bountylabs/blocks-with-screens/pcb/blocks-with-screens.sch

## EAGLE design pcb/blocks-with-screens.sch (2019-09-18)

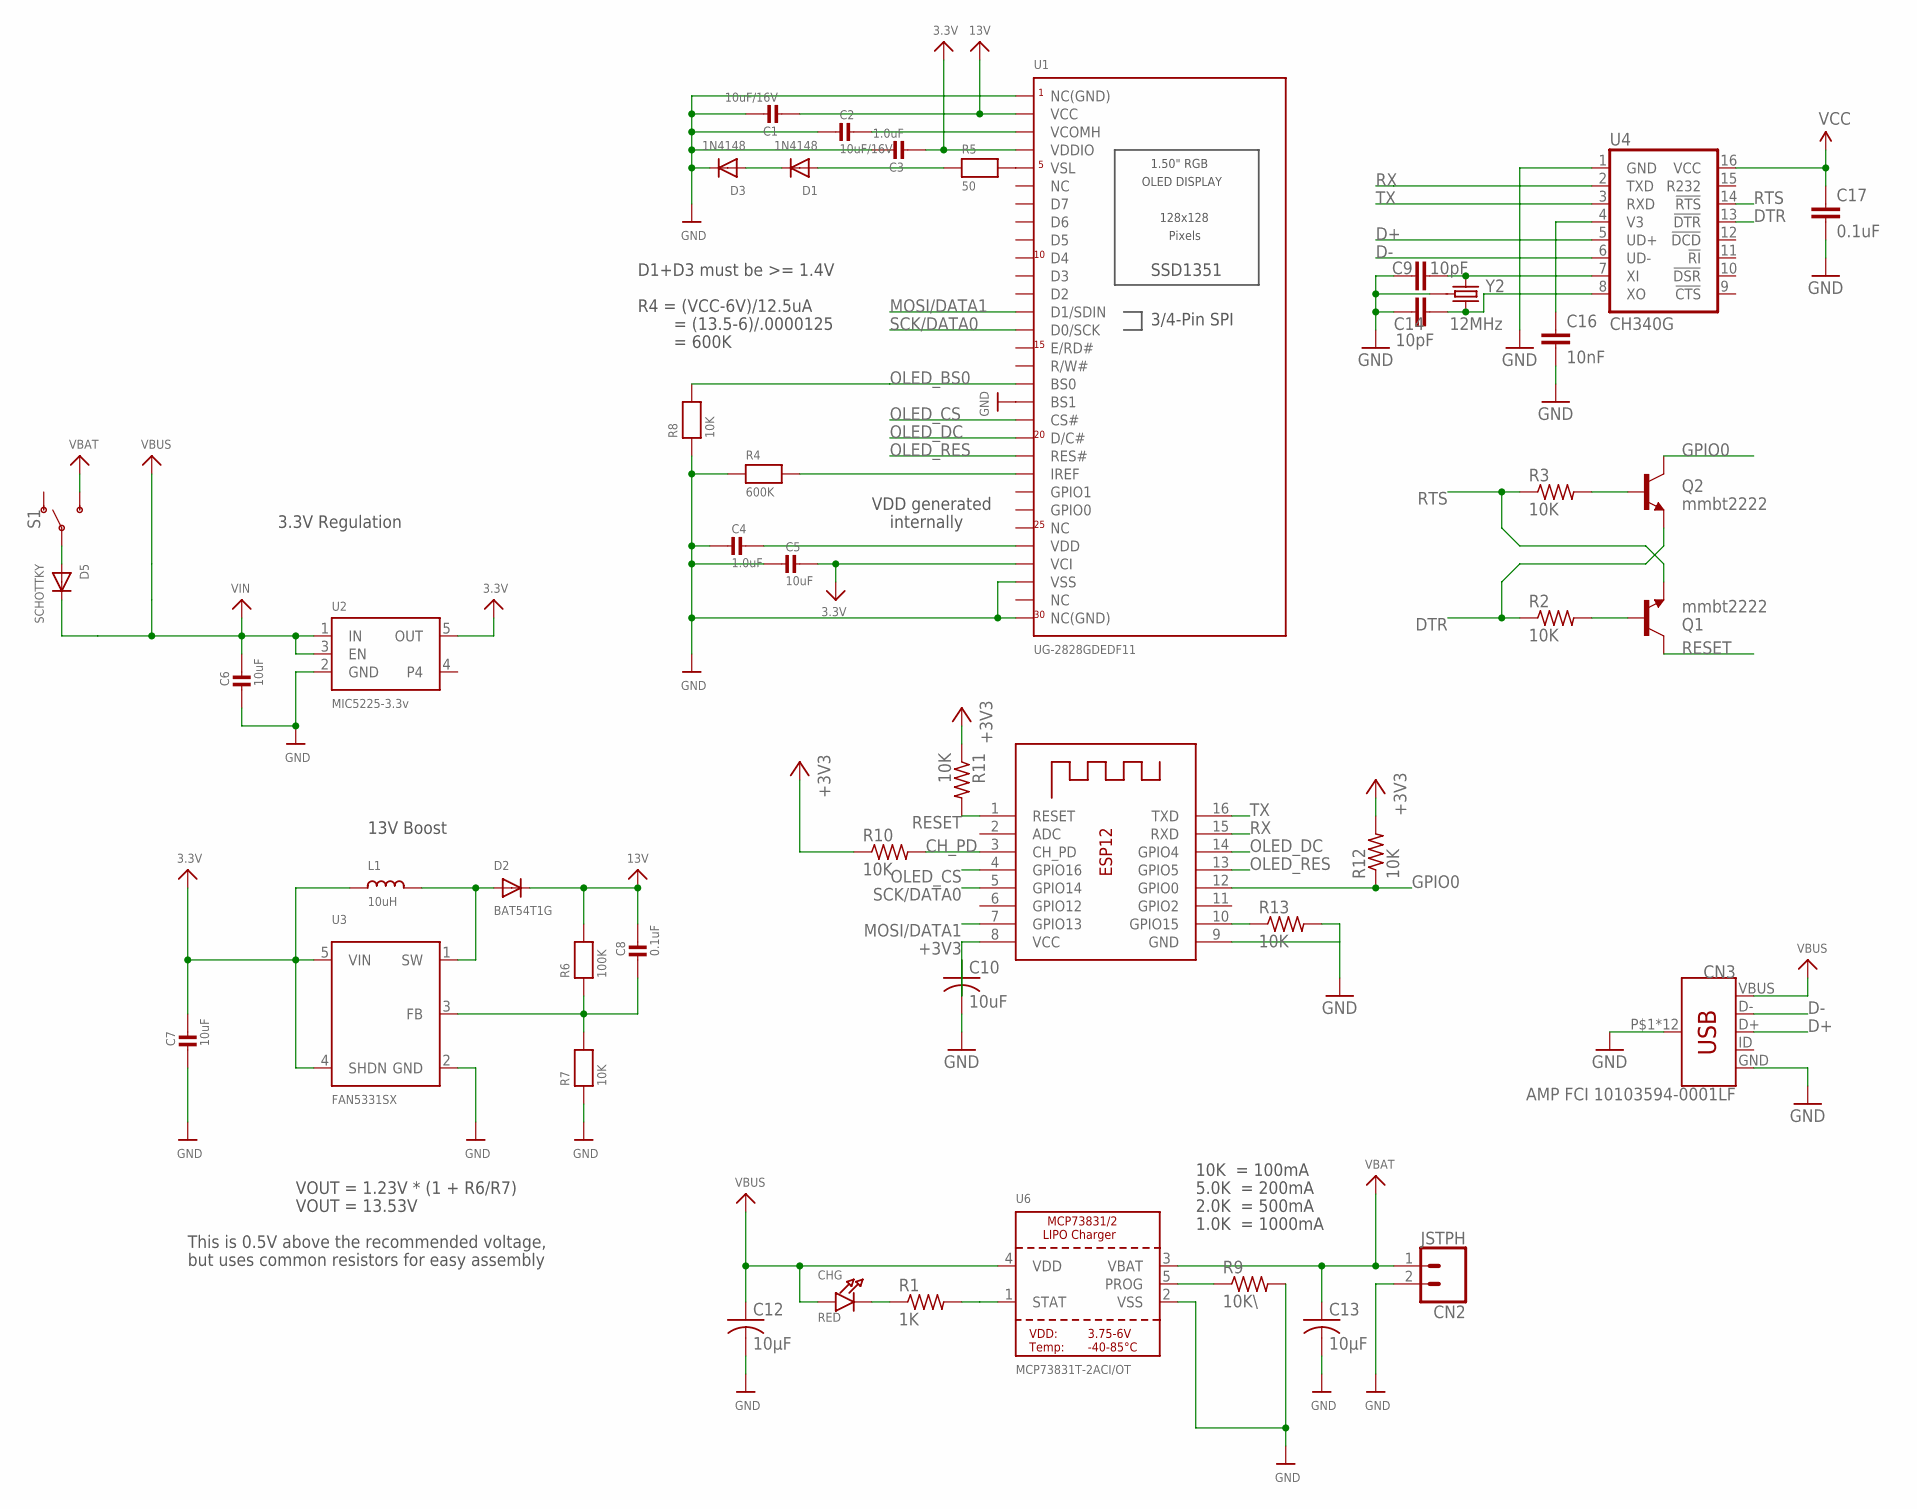
[picture p15: schematic blocks-with-screens.sch]

Parts:
C1, C2: 10uF/16V; 0805
C3, C4: 1.0uF; 0805
C5, C6, C7: 10uF; 0805
C8: 0.1uF; 0805
C9, C14: 10pF; 0603-CAP
C10: 10uF; C0805
C12, C13: 10µF; C0805
C16: 10nF; 0603-CAP
C17: 0.1uF; 0603-CAP
CHG: RED; CHIPLED_0805_NOOUTLINE
CN2: JSTPH; 1X02
CN3: AMP FCI 10103594-0001LF; USB-MICROB-PTH
D1, D3: 1N4148; SOD-323
D2: BAT54T1G; SOD-123
D5: SCHOTTKY; SOD-123FL
L1: 10uH; INDUCTOR_1007
Q1, Q2: mmbt2222; SOT23-3
R1: 1K; R0805
R2, R3: 10K; R0603
R4: 600K; 0805
R5: 50; 0805
R6: 100K; 0805
R7, R8: 10K; 0805
R9: 10K\; R0805
R10, R11, R12, R13: 10K; R0805
S1: SWITCH-SPDT-SMD-RIGHT-ANGLE; SWITCH_SPST_SMD_A
U1: UG-2828GDEDF11; FPC_XF2M-3015-1A
U2: MIC5225-3.3v; SOT23-5
U3: FAN5331SX; SOT23-5@1
U4: CH340G; SO016
U6: MCP73831T-2ACI/OT; SOT23-5
X1: ESP-12
Y2: 12MHz; CRYSTAL-SMD-3.2X2.5

Connections:
3.3V: C3.2, C5.1, C7.1, L1.P$1 (1), U1.P$4 (VCI), U1.P$27 (VDDIO), U2.5 (OUT), U3.4 (SHDN), U3.5 (VIN)
13V: C1.2, C8.1, D2.C, R6.2, U1.P$29 (VCC)
+3V3: C10.1, R10.1, R11.1, R12.2, X1.8 (VCC)
CH_PD: R10.2, X1.3 (CH_PD)
D+: CN3.D+, U4.5 (UD+)
D-: CN3.D-, U4.6 (UD-)
DTR: Q2.2 (E), R2.1, U4.13 (!DTR)
GND: C1.1, C2.2, C3.1, C4.2, C5.2, C6.2, C7.2, C9.1, C10.2, C12.2, C13.2, C14.1, C16.2, C17.2, CN2.2, CN3.GND, CN3.P$1 (SHIELD), D3.C, R4.1, R7.1, R8.1, R9.2, R13.2, U1.P$1 (NC(GND)), U1.P$3 (VSS), U1.P$13 (BS1), U1.P$30 (NC(GND)), U2.2 (GND), U3.2 (GND), U4.1 (GND), U6.2 (VSS), X1.9 (GND), Y2.2 (GND)
GPIO0: Q2.3 (C), R12.1, X1.12 (GPIO0)
IREF: R4.2, U1.P$9 (IREF)
MOSI/DATA1: U1.P$18 (D1/SDIN), X1.7 (GPIO13)
unnamed: CHG.C, R1.1
unnamed: C4.1, U1.P$5 (VDD)
unnamed: R1.2, U6.1 (STAT)
unnamed: D2.A, L1.P$2 (2), U3.1 (SW)
unnamed: R5.2, U1.P$26 (VSL)
unnamed: D1.A, R5.1
unnamed: C8.2, R6.1, R7.2, U3.3 (FB)
unnamed: R9.1, U6.5 (PROG)
unnamed: C14.2, U4.8 (XO), Y2.3 (2)
unnamed: D1.C, D3.A
unnamed: C9.2, U4.7 (XI), Y2.1
unnamed: Q1.1 (B), R2.2
unnamed: Q2.1 (B), R3.2
unnamed: R13.1, X1.10 (GPIO15)
unnamed: D5.A, S1.2
OLED_BS0: R8.2, U1.P$14 (BS0)
OLED_CS: U1.P$12 (CS#), X1.4 (GPIO16)
OLED_DC: U1.P$11 (D/C#), X1.14 (GPIO4)
OLED_RES: U1.P$10 (RES#), X1.13 (GPIO5)
RESET: Q1.3 (C), R11.2, X1.1 (RESET)
RTS: Q1.2 (E), R3.1, U4.14 (!RTS)
RX: U4.2 (TXD), X1.15 (RXD)
SCK/DATA0: U1.P$17 (D0/SCK), X1.5 (GPIO14)
TX: U4.3 (RXD), X1.16 (TXD)
V3: C16.1, U4.4 (V3)
VBAT: C13.1, CN2.1, S1.3 (S), U6.3 (VBAT)
VBUS: C6.1, C12.1, CHG.A, CN3.VBUS, D5.C, U2.1 (IN), U2.3 (EN), U6.4 (VDD)
VCC: C17.1, U4.16 (VCC)
VCOMH: C2.1, U1.P$28 (VCOMH)

Notes on the sheet:
3.3V Regulation
VOUT = 1.23V * (1 + R6/R7)
VOUT = 13.53V
This is 0.5V above the recommended voltage,
but uses common resistors for easy assembly
13V Boost
R4 = (VCC-6V)/12.5uA
= (13.5-6)/.0000125
= 600K
D1+D3 must be >= 1.4V
VDD generated
internally
10K = 100mA
5.0K = 200mA
2.0K = 500mA
1.0K = 1000mA
