bountylabs/blocks-with-screens/blockware/snake/src/main.cpp

#include <Adafruit_GFX.h>
#include <Adafruit_SSD1351.h>
#include <ESP8266WebServer.h>
#include <ESP8266WiFi.h>
#include <DefaultConfig.h>

#define BLUE 0xFF
#define RED 0xF800
#define MESSAGE_SPEED 2
#define INITIAL_SNAKE_LENGTH 1
#define SCALE_FACTOR 8
#define BOARD_SIZE 8
#define UP 1
#define RIGHT 2
#define DOWN 3
#define LEFT 4
#define HTML "<title>Snake</title><meta content=\"width=device-width,initial-scale=1\"name=viewport><script>function makeRequest(e){request=new XMLHttpRequest,request.open(\"GET\",e),request.send()}document.onkeydown=function(e){\"38\"==(e=e||window.event).keyCode?makeRequest(\"/up.html\"):\"40\"==e.keyCode?makeRequest(\"/down.html\"):\"37\"==e.keyCode?makeRequest(\"/left.html\"):\"39\"==e.keyCode&&makeRequest(\"/right.html\")}</script><style>body{position:relative;width:100%;min-height:100vh;min-height:-webkit-fill-available;font-size:32px;font-family:Futura;padding:0;margin:0}.container{position:relative;text-align:center;margin:auto;top:50%;transform:translateY(-50%)}button{display:inline-block;width:50px;height:50px;border-radius:25px;color:#fff;outline:0;border:none;margin-bottom:20px;font-family:Futura}button:active{opacity:.5}.up{background:#466cb2}.down{background:#e1b551;margin-left:20px;margin-right:20px}.left{background:#16a674}.right{background:#ee565d}</style><div class=container>Snake<br><br><button class=up onclick='makeRequest(\"/up.html\")'>Up</button><br><button class=left onclick='makeRequest(\"/left.html\")'>Left</button> <button class=down onclick='makeRequest(\"/down.html\")'>Down</button> <button class=right onclick='makeRequest(\"/right.html\")'>Right</button></div>"

/**
 * Forward defines because C++
 */
void drawGameBoardCell(int oldX, int oldY, byte on);
void unrollSnake();
void showScoreMessage(int score);
void fixEdge();
void handleRight();
void handleLeft();
void handleUp();
void handleDown();
void handleRoot();

/**
 * Bitmaps
 */
const PROGMEM bool snakeMessage[8][56] = {
  {0, 0, 0, 0, 0, 0, 0, 0, 0, 0, 0, 0, 0, 0, 0, 0, 0, 0, 0, 0, 0, 0, 0, 0, 0, 0, 0, 0, 0, 0, 0, 0, 0, 0, 0, 0, 0, 0, 0, 0, 0, 0, 0, 0, 0, 0, 0, 0, 0, 0, 0, 0, 0, 0, 0, 0},
  {0, 0, 0, 0, 0, 0, 0, 0, 0, 1, 1, 1, 1, 0, 0, 0, 1, 1, 0, 0, 0, 1, 1, 0, 0, 0, 1, 1, 1, 1, 0, 0, 0, 1, 1, 0, 0, 1, 1, 0, 0, 1, 1, 1, 1, 1, 1, 0, 0, 0, 0, 0, 0, 0, 0, 0},
  {0, 0, 0, 0, 0, 0, 0, 0, 1, 1, 0, 0, 1, 1, 0, 0, 1, 1, 1, 0, 0, 1, 1, 0, 0, 1, 1, 0, 0, 1, 1, 0, 0, 1, 1, 0, 1, 1, 0, 0, 0, 1, 1, 0, 0, 0, 0, 0, 0, 0, 0, 0, 0, 0, 0, 0},
  {0, 0, 0, 0, 0, 0, 0, 0, 1, 1, 0, 0, 0, 0, 0, 0, 1, 1, 1, 1, 0, 1, 1, 0, 0, 1, 1, 0, 0, 1, 1, 0, 0, 1, 1, 1, 1, 0, 0, 0, 0, 1, 1, 0, 0, 0, 0, 0, 0, 0, 0, 0, 0, 0, 0, 0},
  {0, 0, 0, 0, 0, 0, 0, 0, 0, 1, 1, 1, 1, 0, 0, 0, 1, 1, 0, 1, 1, 1, 1, 0, 0, 1, 1, 1, 1, 1, 1, 0, 0, 1, 1, 1, 0, 0, 0, 0, 0, 1, 1, 1, 1, 1, 0, 0, 0, 0, 0, 0, 0, 0, 0, 0},
  {0, 0, 0, 0, 0, 0, 0, 0, 0, 0, 0, 0, 1, 1, 0, 0, 1, 1, 0, 0, 1, 1, 1, 0, 0, 1, 1, 0, 0, 1, 1, 0, 0, 1, 1, 1, 1, 0, 0, 0, 0, 1, 1, 0, 0, 0, 0, 0, 0, 0, 0, 0, 0, 0, 0, 0},
  {0, 0, 0, 0, 0, 0, 0, 0, 1, 1, 0, 0, 1, 1, 0, 0, 1, 1, 0, 0, 0, 1, 1, 0, 0, 1, 1, 0, 0, 1, 1, 0, 0, 1, 1, 0, 1, 1, 0, 0, 0, 1, 1, 0, 0, 0, 0, 0, 0, 0, 0, 0, 0, 0, 0, 0},
  {0, 0, 0, 0, 0, 0, 0, 0, 0, 1, 1, 1, 1, 0, 0, 0, 1, 1, 0, 0, 0, 1, 1, 0, 0, 1, 1, 0, 0, 1, 1, 0, 0, 1, 1, 0, 0, 1, 1, 0, 0, 1, 1, 1, 1, 1, 1, 0, 0, 0, 0, 0, 0, 0, 0, 0}
};

const PROGMEM bool gameOverMessage[8][90] = {
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
  {0, 0, 0, 0, 0, 0, 0, 0, 0, 1, 1, 1, 1, 0, 0, 0, 0, 1, 1, 1, 1, 0, 0, 0, 0, 1, 1, 1, 1, 0, 0, 0, 1, 1, 0, 0, 1, 1, 0, 0, 1, 1, 1, 1, 1, 1, 0, 0, 0, 0, 0, 0, 0, 0, 0, 0, 0, 0}
};

const PROGMEM bool digits[][8][8] = {
  {
    {0, 0, 0, 0, 0, 0, 0, 0},
    {0, 0, 1, 1, 1, 1, 0, 0},
    {0, 1, 1, 0, 0, 1, 1, 0},
    {0, 1, 1, 0, 1, 1, 1, 0},
    {0, 1, 1, 1, 0, 1, 1, 0},
    {0, 1, 1, 0, 0, 1, 1, 0},
    {0, 1, 1, 0, 0, 1, 1, 0},
    {0, 0, 1, 1, 1, 1, 0, 0}
  },
  {
    {0, 0, 0, 0, 0, 0, 0, 0},
    {0, 0, 0, 1, 1, 0, 0, 0},
    {0, 0, 0, 1, 1, 0, 0, 0},
    {0, 0, 1, 1, 1, 0, 0, 0},
    {0, 0, 0, 1, 1, 0, 0, 0},
    {0, 0, 0, 1, 1, 0, 0, 0},
    {0, 0, 0, 1, 1, 0, 0, 0},
    {0, 1, 1, 1, 1, 1, 1, 0}
  },
  {
    {0, 0, 0, 0, 0, 0, 0, 0},
    {0, 0, 1, 1, 1, 1, 0, 0},
    {0, 1, 1, 0, 0, 1, 1, 0},
    {0, 0, 0, 0, 0, 1, 1, 0},
    {0, 0, 0, 0, 1, 1, 0, 0},
    {0, 0, 1, 1, 0, 0, 0, 0},
    {0, 1, 1, 0, 0, 0, 0, 0},
    {0, 1, 1, 1, 1, 1, 1, 0}
  },
  {
    {0, 0, 0, 0, 0, 0, 0, 0},
    {0, 0, 1, 1, 1, 1, 0, 0},
    {0, 1, 1, 0, 0, 1, 1, 0},
    {0, 0, 0, 0, 0, 1, 1, 0},
    {0, 0, 0, 1, 1, 1, 0, 0},
    {0, 0, 0, 0, 0, 1, 1, 0},
    {0, 1, 1, 0, 0, 1, 1, 0},
    {0, 0, 1, 1, 1, 1, 0, 0}
  },
  {
    {0, 0, 0, 0, 0, 0, 0, 0},
    {0, 0, 0, 0, 1, 1, 0, 0},
    {0, 0, 0, 1, 1, 1, 0, 0},
    {0, 0, 1, 0, 1, 1, 0, 0},
    {0, 1, 0, 0, 1, 1, 0, 0},
    {0, 1, 1, 1, 1, 1, 1, 0},
    {0, 0, 0, 0, 1, 1, 0, 0},
    {0, 0, 0, 0, 1, 1, 0, 0}
  },
  {
    {0, 0, 0, 0, 0, 0, 0, 0},
    {0, 1, 1, 1, 1, 1, 1, 0},
    {0, 1, 1, 0, 0, 0, 0, 0},
    {0, 1, 1, 1, 1, 1, 0, 0},
    {0, 0, 0, 0, 0, 1, 1, 0},
    {0, 0, 0, 0, 0, 1, 1, 0},
    {0, 1, 1, 0, 0, 1, 1, 0},
    {0, 0, 1, 1, 1, 1, 0, 0}
  },
  {
    {0, 0, 0, 0, 0, 0, 0, 0},
    {0, 0, 1, 1, 1, 1, 0, 0},
    {0, 1, 1, 0, 0, 1, 1, 0},
    {0, 1, 1, 0, 0, 0, 0, 0},
    {0, 1, 1, 1, 1, 1, 0, 0},
    {0, 1, 1, 0, 0, 1, 1, 0},
    {0, 1, 1, 0, 0, 1, 1, 0},
    {0, 0, 1, 1, 1, 1, 0, 0}
  },
  {
    {0, 0, 0, 0, 0, 0, 0, 0},
    {0, 1, 1, 1, 1, 1, 1, 0},
    {0, 1, 1, 0, 0, 1, 1, 0},
    {0, 0, 0, 0, 1, 1, 0, 0},
    {0, 0, 0, 0, 1, 1, 0, 0},
    {0, 0, 0, 1, 1, 0, 0, 0},
    {0, 0, 0, 1, 1, 0, 0, 0},
    {0, 0, 0, 1, 1, 0, 0, 0}
  },
  {
    {0, 0, 0, 0, 0, 0, 0, 0},
    {0, 0, 1, 1, 1, 1, 0, 0},
    {0, 1, 1, 0, 0, 1, 1, 0},
    {0, 1, 1, 0, 0, 1, 1, 0},
    {0, 0, 1, 1, 1, 1, 0, 0},
    {0, 1, 1, 0, 0, 1, 1, 0},
    {0, 1, 1, 0, 0, 1, 1, 0},
    {0, 0, 1, 1, 1, 1, 0, 0}
  },
  {
    {0, 0, 0, 0, 0, 0, 0, 0},
    {0, 0, 1, 1, 1, 1, 0, 0},
    {0, 1, 1, 0, 0, 1, 1, 0},
    {0, 1, 1, 0, 0, 1, 1, 0},
    {0, 0, 1, 1, 1, 1, 1, 0},
    {0, 0, 0, 0, 0, 1, 1, 0},
    {0, 1, 1, 0, 0, 1, 1, 0},
    {0, 0, 1, 1, 1, 1, 0, 0}
  }
};

/**
 * Global variables.
 */
ESP8266WebServer server(80);
IPAddress IP(192,168,4,15);
IPAddress mask = (255, 255, 255, 0);
int connected = 0;
Adafruit_SSD1351 display = Adafruit_SSD1351(SCREEN_WIDTH, SCREEN_HEIGHT, &SPI, CS_PIN, DC_PIN, RST_PIN);

struct Point {
  int row = 0, col = 0;
  Point(int row = 0, int col = 0): row(row), col(col) {}
};

/**
 * Game state
 */
int gameboard[BOARD_SIZE][BOARD_SIZE] = {};
bool win = false;
bool gameOver = false;
Point snake;  // primary snake head coordinates (snake head), it will be randomly generated
Point food(-1, -1); // food is not anywhere yet

/**
 * Snake parameters
 */
int snakeLength = INITIAL_SNAKE_LENGTH; // choosed by the user in the config section
int snakeSpeed = 1; // will be set according to potentiometer value, cannot be 0
int snakeDirection = 0; // if it is 0, the snake does not move

/**
 * Sets up WiFi for the block. This enables the block to serve as the access point.
 */
void setUpWifi() {
  WiFi.mode(WIFI_AP);
  WiFi.softAP("Snake", "");
  WiFi.softAPConfig(IP, IP, mask);
}

/**
 * Sets up Web server routing. The web pages listed will be used to serve pages that
 * clients can visit to control the snake.
 */
void setUpRouting() {
  server.on("/", handleRoot);
  server.on("/up.html", handleUp);
  server.on("/down.html", handleDown);
  server.on("/left.html", handleLeft);
  server.on("/right.html", handleRight);
  server.begin();
}

/**
 * Handles when the client visits "/"
 */
void handleRoot() {
  connected = 1;
  server.send(200, "text/html", HTML);
}


/**
 * Handles when the client visits "/up"
 */
void handleUp() {
  snakeDirection = UP;
  server.send(200, "text/html", HTML);
}

/**
 * Handles when the client visits "/down"
 */
void handleDown() {
  snakeDirection = DOWN;
  server.send(200, "text/html", HTML);
}

/**
 * Handles when the client visits "/left"
 */
void handleLeft() {
  snakeDirection = LEFT;
  server.send(200, "text/html", HTML);
}

/**
 * Handles when the client visits "/right"
 */
void handleRight() {
  snakeDirection = RIGHT;
  server.send(200, "text/html", HTML);
}

/**
 * Initializes the game
 */
void initializeGame() {
  randomSeed(analogRead(A0));
  snake.row = random(8);
  snake.col = random(8);
}

/**
 * Shows the bootscreen.
 */
void showSnakeMessage() {
  [&] {
    for (int d = 0; d < sizeof(snakeMessage[0]) - 7; d++) {
      for (int col = 0; col < 8; col++) {
        delay(MESSAGE_SPEED);
        for (int row = 0; row < 8; row++) {
          // this reads the byte from the PROGMEM and displays it on the screen
          drawGameBoardCell(row, col, pgm_read_byte(&(snakeMessage[row][col + d])));
        }
        if (connected) {
          return;
        }
      }
    }
  }();
}

/**
 * Generates a food cell if one does not already exist.
 */
void generateFood() {
  if (food.row == -1 || food.col == -1) {
    // self-explanatory
    if (snakeLength >= 64) {
      win = true;
      return; // prevent the food generator from running, in this case it would run forever, because it will not be able to find a pixel without a snake
    }

    // generate food until it is in the right position
    do {
      food.col = random(8);
      food.row = random(8);
    } while (gameboard[food.row][food.col] > 0);
  }
}


/**
 * Changes movement of the snake to react to user input.
 */
void reactToInput() {
  int previousDirection = snakeDirection; // save the last direction

  delay(snakeSpeed);
  
  // ignore directional change by 180 degrees (no effect for non-moving snake)
  snakeDirection + 2 == previousDirection && previousDirection != 0 ? snakeDirection = previousDirection : 0;
  snakeDirection - 2 == previousDirection && previousDirection != 0 ? snakeDirection = previousDirection : 0;
  
  // intelligently blink with the food
  drawGameBoardCell(food.row, food.col, millis() % 100 < 50 ? 1 : 0);
}

/**
 * Calculates location of snake.
 */
void calculateSnake() {
   // decrement all the snake body segments, if segment is 0, turn the corresponding led off
  for (int row = 0; row < 8; row++) {
    for (int col = 0; col < 8; col++) {
      // if there is a body segment, decrement it's value
      if (gameboard[row][col] > 0 ) {
        gameboard[row][col]--;
      }

      // display the current pixel
      drawGameBoardCell(row, col, gameboard[row][col] == 0 ? 0 : 1);
    }
  }
  
  switch (snakeDirection) {
    case UP: {
      snake.row--;
      fixEdge();
      drawGameBoardCell(snake.row, snake.col, 1);
      break;
    }
    case RIGHT: {
      snake.col++;
      fixEdge();
      drawGameBoardCell(snake.row, snake.col, 1);
      break;
    }
    case DOWN: {
      snake.row++;
      fixEdge();
      drawGameBoardCell(snake.row, snake.col, 1);
      break;
    }
    case LEFT: {
      snake.col--;
      fixEdge();
      drawGameBoardCell(snake.row, snake.col, 1);
      break;
    }
    default: {
      return;
    }
  }

  // if there is a snake body segment, this will cause the end of the game (snake must be moving)
  if (gameboard[snake.row][snake.col] > 1 && snakeDirection != 0) {
    gameOver = true;
    return;
  }

  // check if the food was eaten
  if (snake.row == food.row && snake.col == food.col) {
    food.row = -1; // reset food
    food.col = -1;

    // increment snake length
    snakeLength++;

    // increment all the snake body segments
    for (int row = 0; row < 8; row++) {
      for (int col = 0; col < 8; col++) {
        if (gameboard[row][col] > 0 ) {
          gameboard[row][col]++;
        }
      }
    }
  }

  // add new segment at the snake head location
  gameboard[snake.row][snake.col] = snakeLength + 1; // will be decremented in a moment
}

/**
 * Handles a change in the game's state and displays appropriate messages if necessary.
 */
void handleGameStates() {
  if (gameOver || win) {
    unrollSnake();

    showScoreMessage(snakeLength - INITIAL_SNAKE_LENGTH);
    
    // re-init the game
    win = false;
    gameOver = false;
    snake.row = random(8);
    snake.col = random(8);
    food.row = -1;
    food.col = -1;
    snakeLength = INITIAL_SNAKE_LENGTH;
    snakeDirection = 0;
    memset(gameboard, 0, sizeof(gameboard[0][0]) * 8 * 8);
  }
}

/**
 * Runs the game loop. Call this on every loop() iteration once the client has
 * connected.
 */
void runGameLoop() {
  generateFood();     // if there is no food, generate one
  reactToInput();     // watches joystick movements & blinks with food
  calculateSnake();   // calculates snake parameters
  handleGameStates();
}

/**
 * Draws the specified cell in the game board along with whether it is on or
 * off to the screen. 
 */
void drawGameBoardCell(int oldX, int oldY, byte on) {
  int x = oldY;
  int y = oldX;

  int xOffset = (display.width() - (SCALE_FACTOR * BOARD_SIZE)) / 2;
  int yOffset = (display.height() - (SCALE_FACTOR * BOARD_SIZE)) / 2;

  for (int pixelX = 0; pixelX < SCALE_FACTOR / 2; pixelX++) {
    for (int pixelY = 0; pixelY < SCALE_FACTOR / 2; pixelY++) {
      display.drawPixel(SCALE_FACTOR * x + pixelX + xOffset, SCALE_FACTOR * y + pixelY + yOffset, on == 0 ? 0x00 :0xFF);
    }
  }
}

/**
 * Draws the bounds of the game board.
 */
void drawBounds() {
  int xOffset = (display.width() - (SCALE_FACTOR * BOARD_SIZE)) / 2;
  int yOffset = (display.height() - (SCALE_FACTOR * BOARD_SIZE)) / 2;
  
  for (int pixelY = 0; pixelY < display.height(); pixelY++) {
    display.drawPixel(xOffset - 1, pixelY, RED);
  }

  for (int pixelY = 0; pixelY < display.height(); pixelY++) {
    display.drawPixel(display.width() - xOffset, pixelY, RED);
  }

  for (int pixelX = 0; pixelX < display.width(); pixelX++) {
    display.drawPixel(pixelX, yOffset - 1, RED);
  }

  for (int pixelX = 0; pixelX < display.width(); pixelX++) {
    display.drawPixel(pixelX, display.height() - yOffset, RED);
  }
}

/**
 * Wraps the snake to the other side of the screen if needed.
 */
void fixEdge() {
  snake.col < 0 ? snake.col += 8 : 0;
  snake.col > 7 ? snake.col -= 8 : 0;
  snake.row < 0 ? snake.row += 8 : 0;
  snake.row > 7 ? snake.row -= 8 : 0;
}

/**
 * Unrolls the snake.
 */
void unrollSnake() {
  // switch off the food LED
  drawGameBoardCell(food.row, food.col, 0);
  delay(800);
  // flash the screen 5 times
  for (int i = 0; i < 5; i++) {
    // invert the screen
    for (int row = 0; row < 8; row++) {
      for (int col = 0; col < 8; col++) {
        drawGameBoardCell(row, col, gameboard[row][col] == 0 ? 1 : 0);
      }
    }
    delay(20);
    // invert it back
    for (int row = 0; row < 8; row++) {
      for (int col = 0; col < 8; col++) {
        drawGameBoardCell(row, col, gameboard[row][col] == 0 ? 0 : 1);
      }
    }
    delay(50);
  }
  delay(600);
  for (int i = 1; i <= snakeLength; i++) {
    for (int row = 0; row < 8; row++) {
      for (int col = 0; col < 8; col++) {
        if (gameboard[row][col] == i) {
          drawGameBoardCell(row, col, 0);
          delay(100);
        }
      }
    }
  }
}

/**
 * Shows the score message along with the score once the game is over.
 */
void showScoreMessage(int score) {
  if (score < 0 || score > 99) return;

  // specify score digits
  int second = score % 10;
  int first = (score / 10) % 10;

  [&] {
    for (int d = 0; d < sizeof(scoreMessage[0]) + 2 * sizeof(digits[0][0]); d++) {
      for (int col = 0; col < 8; col++) {
        delay(MESSAGE_SPEED);
        for (int row = 0; row < 8; row++) {
          if (d <= sizeof(scoreMessage[0]) - 8) {
            drawGameBoardCell(row, col, pgm_read_byte(&(scoreMessage[row][col + d])));
          }

          int c = col + d - sizeof(scoreMessage[0]) + 6; // move 6 px in front of the previous message

          // if the score is < 10, shift out the first digit (zero)
          if (score < 10) c += 8;

          if (c >= 0 && c < 8) {
            if (first > 0) drawGameBoardCell(row, col, pgm_read_byte(&(digits[first][row][c]))); // show only if score is >= 10 (see above)
          } else {
            c -= 8;
            if (c >= 0 && c < 8) {
              drawGameBoardCell(row, col, pgm_read_byte(&(digits[second][row][c]))); // show always
            }
          }
        }
      }
    }
  }();
}

/**
 * Maps a value in an interval of floats to another interval of floats.
 */
float mapf(float x, float in_min, float in_max, float out_min, float out_max) {
  return (x - in_min) * (out_max - out_min) / (in_max - in_min) + out_min;
}

void setup() {
  Serial.begin(9600);  // set the same baud rate on your Serial Monitor

  display.begin();
  display.fillScreen(0x00);

  setUpWifi();
  setUpRouting();
  
  initializeGame();     // initialize pins & LED matrix
  showSnakeMessage();   // scrolls the 'snake' message around the matrix
  drawBounds();
}

void loop() {
  server.handleClient();
  if (!connected) {
    return;
  }
  runGameLoop();
}
