bountylabs/blocks-with-screens/blockware/fireworks/src/TLLogos.h

unsigned char tl_blue[] = {
  0x00, 0x00, 0x00, 0x00, 0x00, 0x00, 0x00, 0x00, 0x00, 0x00, 0x00, 0x00, 0x00,
  0x00, 0x00, 0x00, 0x00, 0x00, 0x00, 0x00, 0x00, 0x00, 0x00, 0x00, 0x00, 0x00,
  0x00, 0x00, 0x00, 0x00, 0x00, 0x00, 0x00, 0x00, 0x00, 0x00, 0x00, 0x00, 0x00,
  0x00, 0x00, 0x00, 0x00, 0x00, 0x66, 0x00, 0xd4, 0x43, 0xfd, 0x1c, 0xfe, 0x1c,
  0x1d, 0x25, 0xdd, 0x1c, 0x1e, 0x1d, 0xfe, 0x1c, 0xfd, 0x1c, 0xfe, 0x1c, 0x00,
  0x00, 0x00, 0x00, 0x00, 0x00, 0x00, 0x00, 0x00, 0x00, 0x00, 0x00, 0xf3, 0x4b,
  0x66, 0x00, 0x00, 0x00, 0x00, 0x00, 0x35, 0x4c, 0x86, 0x00, 0x00, 0x00, 0x00,
  0x00, 0x00, 0x00, 0x00, 0x00, 0x00, 0x00, 0x00, 0x00, 0x00, 0x00, 0x00, 0x00,
  0x00, 0x00, 0x00, 0x00, 0x00, 0x00, 0x00, 0x00, 0x00, 0x00, 0x00, 0x00, 0x00,
  0x00, 0x00, 0x00, 0x00, 0x00, 0x00, 0x00, 0xbc, 0x14, 0xfd, 0x24, 0xfe, 0x1c,
  0x1d, 0x1d, 0xfe, 0x1c, 0x1d, 0x1d, 0xfe, 0x1c, 0x1d, 0x1d, 0xfe, 0x1c, 0x1d,
  0x1d, 0x56, 0x4c, 0x86, 0x00, 0x00, 0x00, 0x00, 0x00, 0xbc, 0x1c, 0xfc, 0x24,
  0x76, 0x4c, 0x86, 0x00, 0x86, 0x00, 0x76, 0x4c, 0x1d, 0x1d, 0xfe, 0x1c, 0x00,
  0x00, 0x00, 0x00, 0x00, 0x00, 0x00, 0x00, 0x00, 0x00, 0x00, 0x00, 0x00, 0x00,
  0x00, 0x00, 0x00, 0x00, 0x00, 0x00, 0x00, 0x00, 0x00, 0x00, 0x00, 0x00, 0x00,
  0x00, 0x00, 0x00, 0x00, 0x00, 0x87, 0x00, 0x97, 0x4c, 0x1e, 0x1d, 0x1e, 0x1d,
  0x1e, 0x1d, 0x1e, 0x1d, 0x1e, 0x1d, 0x1e, 0x1d, 0x1e, 0x1d, 0x1e, 0x1d, 0x1e,
  0x1d, 0x1e, 0x1d, 0x1e, 0x1d, 0xfe, 0x1c, 0x1e, 0x1d, 0x1e, 0x1d, 0x1e, 0x1d,
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
  0x28, 0x8d, 0xdd, 0x63, 0xfd, 0x64, 0xfd, 0x63, 0xfd, 0x64, 0xfd, 0x63, 0xfd,
  0x64, 0xfd, 0x64, 0xfd, 0x03, 0xed, 0x00, 0x00, 0x00, 0x00, 0x00, 0x00, 0x00,
  0x00, 0x00, 0x00, 0x00, 0x00, 0x00, 0x00, 0x00, 0x00, 0x00, 0x28, 0x8d, 0xdd,
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
