bountylabs/blocks-with-screens/blockware/stocks-and-weather/src/httphelper.cpp

#include <Arduino.h>

String getHttpGETRequestWithUrlAndHost(String host, String url) {
  return String("GET ") + url + " HTTP/1.1\r\n" +
         "Host: " + host + "\r\n" +
         "Connection: close\r\n\r\n";
}
